mitmedialab/doodlebot/images/step9_img1.jpg

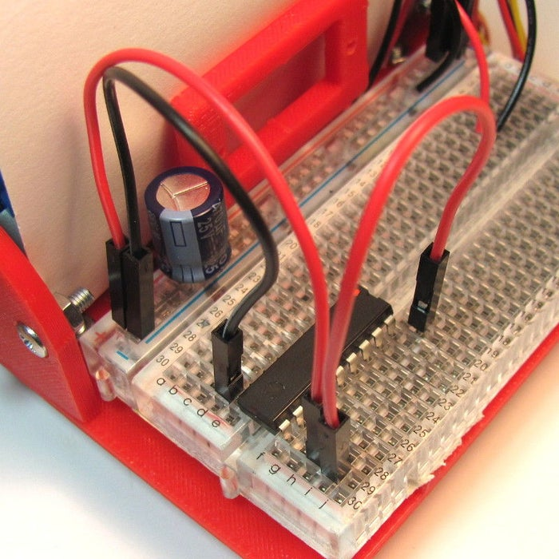
images/step9_img1.jpg
